0xbabayaga/DDOZER/firmware/src/drivers/ascii.h

#ifndef _ASCI_H
#define _ASCI_H

#include "../base/types.h"

#define  SMALL_FONT_WIDTH       5
#define  SMALL_FONT_HEIGHT      8

#define  FONT16_SYMBOL_SIZE     33
#define  FONT16_SYMBOL_NUM      96

#define  ICON_WIDTH             16
#define  ICON_HEIGHT            16
#define  ICON_MARGIN            4 

typedef enum _eIcon
{
    eIcon_None = -1,
    eIcon_Back = 0,
    eIcon_Cancel = 1,
    eIcon_Ok = 2,
    eIcon_Total = 3
}   eIcon;

static const uint8 ICONS[eIcon_Total][ICON_WIDTH * ICON_HEIGHT / 2] = 
{
    {   //Back arrow icon
        0x00,   0x80,   0xC0,   0xA0,   0x90,   0x88,   0x84,   0x82,   0x80,   0x80,   0x80,   0x80,   0x80,   0x00,   0x00,   0x00,
        0x00,   0x01,   0x02,   0x04,   0x08,   0x10,   0x20,   0x40,   0x00,   0x00,   0x00,   0x00,   0x00,   0x00,   0x00,   0x00
    },
    {   //Cancel icon
        0x00,   0x02,   0x04,   0x08,   0x10,   0x20,   0x40,   0x80,   0x40,   0x20,   0x10,   0x08,   0x04,   0x02,   0x00,   0x00,
        0x00,   0x20,   0x10,   0x08,   0x04,   0x02,   0x01,   0x00,   0x01,   0x02,   0x04,   0x08,   0x10,   0x20,   0x00,   0x00,
    },
    {   //Ok icon
        0x00,   0x00,   0x00,   0x00,   0x00,   0x00,   0x00,   0x00,   0x00,   0x80,   0x60,   0x18,   0x06,   0x00,   0x00,   0x00,
        0x00,   0x01,   0x02,   0x04,   0x08,   0x10,   0x20,   0x18,   0x06,   0x01,   0x00,   0x00,   0x00,   0x00,   0x00,   0x00
    }
};



#define  ASCII
/*
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
//?                 - 0xD0
0x7F, 0x11, 0x11, 0x11, 0x0E,
//?                 - 0xD1
0x3E, 0x41, 0x41, 0x41, 0x22,
//?                 - 0xD2
0x01, 0x01, 0x7F, 0x01, 0x01,
//?                 - 0xD3
0x47, 0x48, 0x48, 0x48, 0x3F,
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
};

uint8* ASCII_FontPtr(char c);

#endif
