0xbabayaga/DDOZER/firmware/src/core/strings.h

#ifndef _STRINGS_H
#define _STRINGS_H

#define STR_BACK            "  "
#define STR_DOSING          "DOSING"
#define STR_DATETIME        "DATE/TIME"
#define STR_CALIBRATION     "CALIBRATION"
#define STR_OPTIONS         "OPTIONS"
#define STR_CANCEL          "CANCEL"
#define STR_DAILY_DOSAGE    "DAILY DOSAGE"
#define STR_PORTIONS        "PORTIONS"
#define STR_TIME            "TIME"
#define STR_START_TIME      "START "STR_TIME
#define STR_END_TIME        "END "STR_TIME
#define STR_SAVE            "SAVE"
#define STR_SET             "SET"
#define STR_SET_HOURS       STR_SET" HOURS"
#define STR_SET_MINUTES     STR_SET" MINUTES"
#define STR_SET_SECONDS     STR_SET" SECONDS"
#define STR_SET_DAY     	STR_SET" DAY"
#define STR_SET_MONTH     	STR_SET" MONTH"
#define STR_SET_YEAR     	STR_SET" YEAR"
#define STR_START           "START"
#define STR_VOLUME 			"VOLUME"
#define STR_SET_VOLUME      STR_SET" "STR_VOLUME
#define STR_TEST_VOLUME     "TEST "STR_VOLUME
#define STR_CHECK			"CHECK"
#define STR_MATERIAL        "MATERIAL"
#define STR_SPEED        	"SPEED"
#define STR_LOW        		"LOW"
#define STR_NORMAL        	"NORMAL"
#define STR_HIGH        	"HIGH"
#define STR_ALK  			"ALK"
#define STR_CA 				"CA"
#define STR_MG        		"MG"
#define STR_NO3				"NO3"
#define STR_PO4				"PO4"
#define STR_FOOD			"FOOD"
#define STR_ROTATION		"ROTATION"
#define STR_CW				"CLOCKWISE"
#define STR_ACW				"A"STR_CW
#define STR_RESET			"RESET"
#define STR_DATE 			"DATE"
#define STR_SINCE_CAL		"SINCE CALIBRATION"
#define STR_TOTAL			"TOTAL"
#define STR_STAT            "STATISTICS"
#define STR_START_DATE		STR_START" "STR_DATE
#define STR_UPTIME			"UPTIME"

#define STR_FORMAT_STR      "%s"
#define STR_FORMAT_VOLUME   "%03d.%dml"
#define STR_FORMAT_VOL   	"%02d.%dml"
#define STR_FORMAT_VOLUME_L "%03lu.%luml"
#define STR_FORMAT_VOLUME_S "%03dml"
#define STR_FORMAT_02D      "%02d"
#define STR_FORMAT_09LU     "%09lu"
#define STR_FORMAT_TIMES    STR_FORMAT_02D" times"
#define STR_FORMAT_HH_MM    STR_FORMAT_02D":"STR_FORMAT_02D
#define STR_FORMAT_HH_MM_SS STR_FORMAT_HH_MM":"STR_FORMAT_02D
#define STR_FORMAT_DD_MM_YY STR_FORMAT_02D"."STR_FORMAT_02D"."STR_FORMAT_02D
#define STR_FORMAT_UPTIME   "%03lu.%02lu:%02lu"
    

#endif
